sfranzyshen/kame32/code/src/config.h

#ifndef config_h
#define config_h

#define SSID        "Kame32"
#define PASSWORD    "00000000"
#define HOSTNAME    "kame32"
#define LED_PIN     2

int servo_calibration[8] = {2, -5, -1, 6, 2, -2, 5, 6};

#endif
